Victeldo/footrest-design/versions/v9-trial/artifacts/PRINT_FIRST_V9_rail_coupon.stl

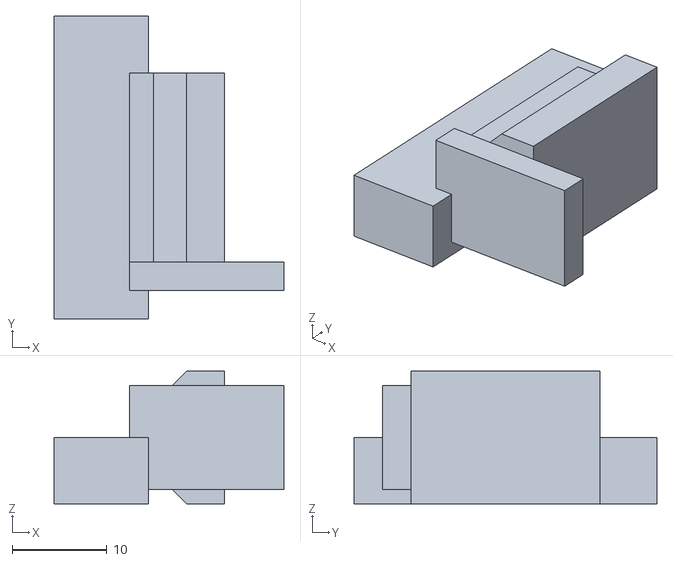
[picture p19: CAD file, 2026-09-20]
versions/v9-trial/artifacts/PRINT_FIRST_V9_rail_coupon.stl
24.3 x 32.0 x 14.0
