Victeldo/footrest-design/versions/v6a/artifacts/reference/footrest_tolerance_coupon_v6_7mm_sockets_only.stl

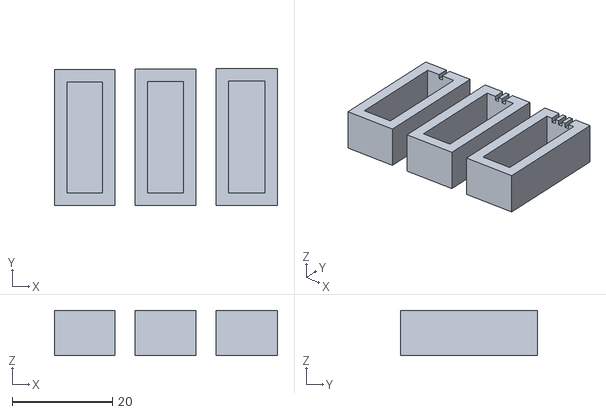
[picture p20: CAD file, 2026-09-20]
versions/v6a/artifacts/reference/footrest_tolerance_coupon_v6_7mm_sockets_only.stl
44.6 x 27.3 x 9.00
