Victeldo/footrest-design/versions/v8b/artifacts/V8B_trial_tongue.stl

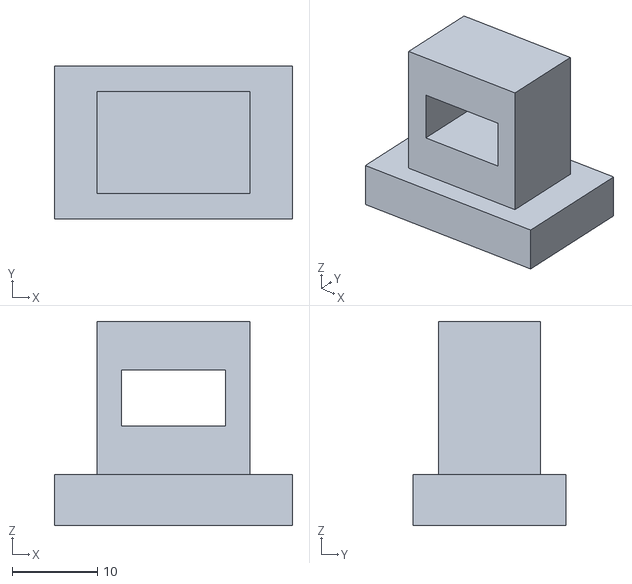
[picture p21: CAD file, 2026-09-20]
versions/v8b/artifacts/V8B_trial_tongue.stl
28.0 x 18.0 x 24.0
