Victeldo/footrest-design/versions/v6a/artifacts/reference/flatpack_footrest_v3_top.stl

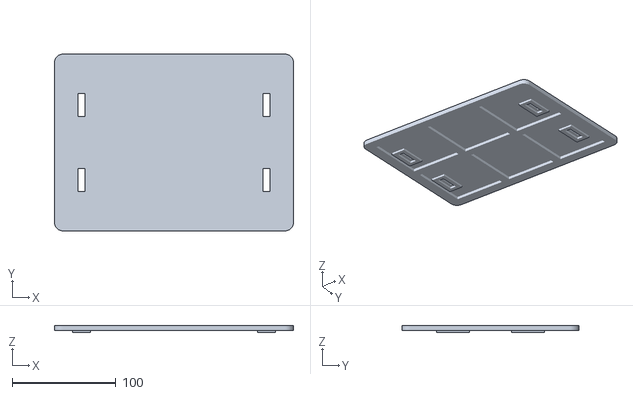
[picture p22: CAD file, 2026-09-20]
versions/v6a/artifacts/reference/flatpack_footrest_v3_top.stl
230.0 x 170.0 x 7.00
