Victeldo/footrest-design/versions/v9-full/artifacts/V9_full_assembly.png

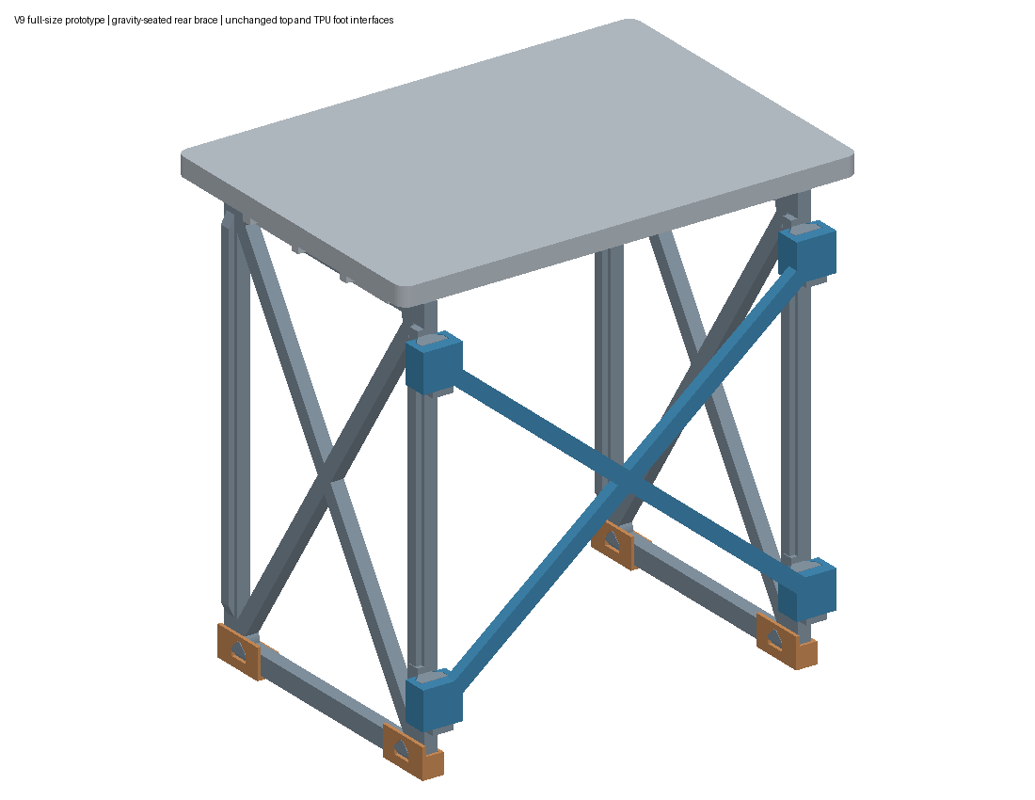
versions/v9-full/artifacts/V9_full_assembly.png
